Pan-Robotics/Robust-IO-Expander/Robust IO Expander/Docs/Photos/3D 2.png

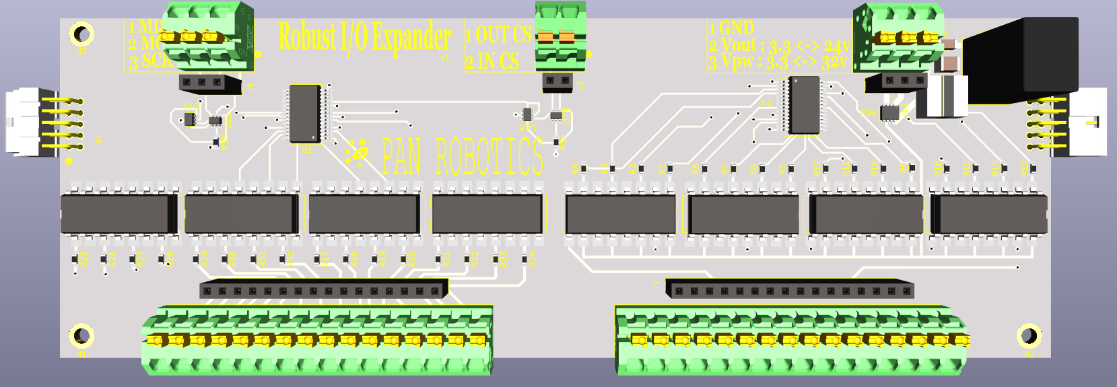
Robust IO Expander/Docs/Photos/3D 2.png
