Pan-Robotics/Robust-IO-Expander/Robust IO Expander/Docs/Photos/3D 3.png

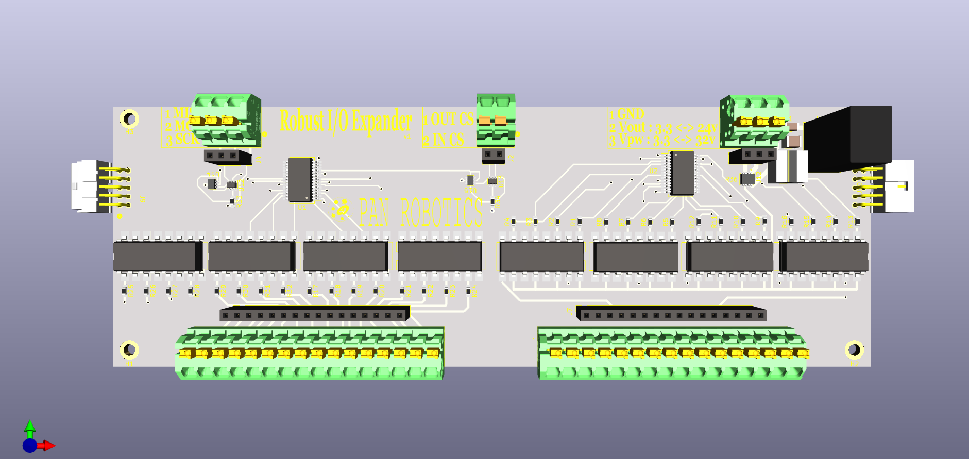
Robust IO Expander/Docs/Photos/3D 3.png
