Pan-Robotics/Robust-IO-Expander/Robust IO Expander/Docs/Photos/3D_2-clear.png

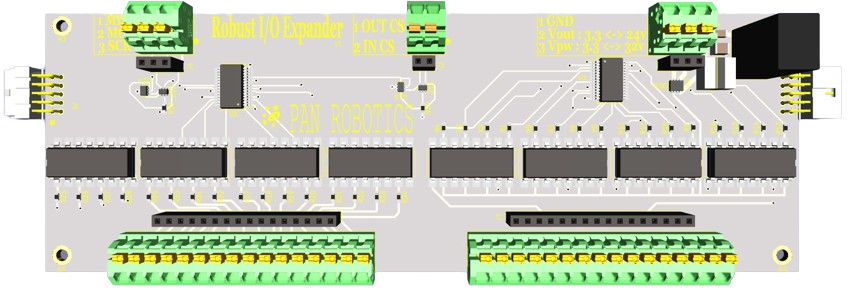
Robust IO Expander/Docs/Photos/3D_2-clear.png
