Pan-Robotics/Robust-IO-Expander/Robust IO Expander/Docs/Photos/3D_5-wacky.png

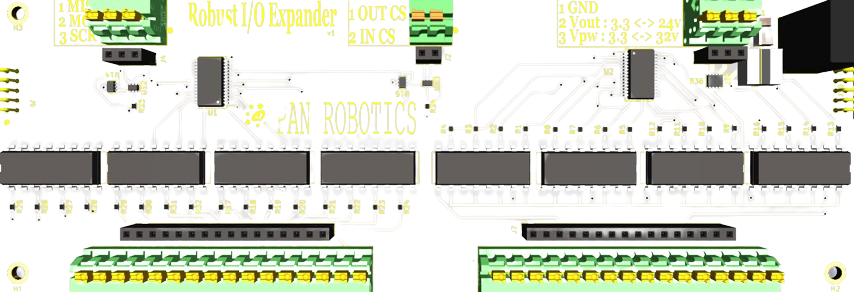
Robust IO Expander/Docs/Photos/3D_5-wacky.png
