Pan-Robotics/Robust-IO-Expander/Robust IO Expander/Docs/Photos/FreeCAD 3D 1.png

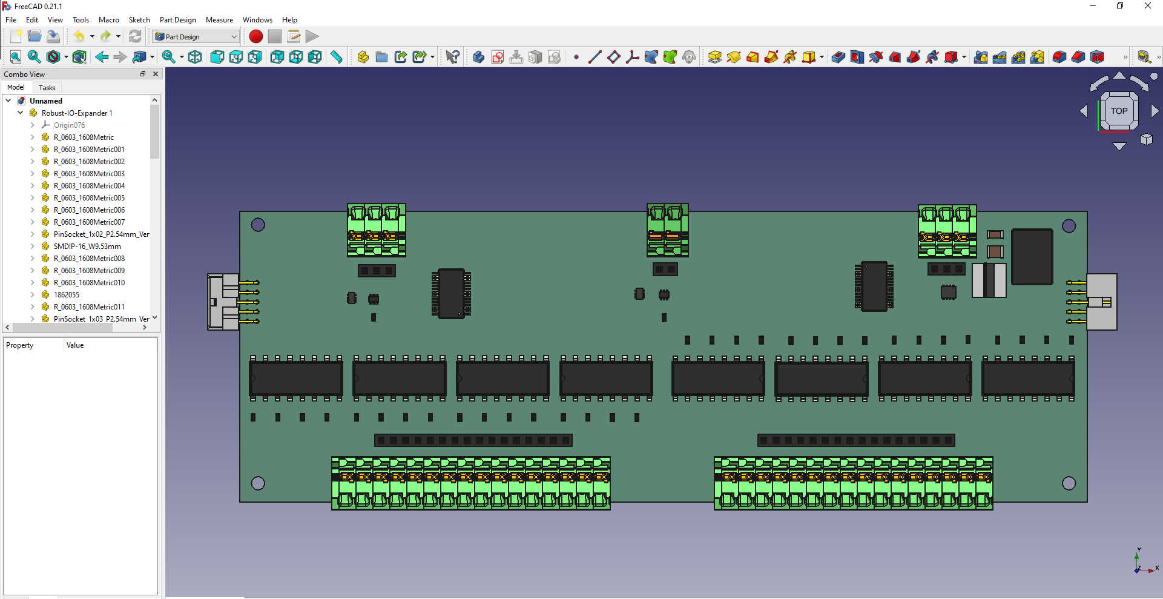
Robust IO Expander/Docs/Photos/FreeCAD 3D 1.png
