Pan-Robotics/Robust-IO-Expander/Robust IO Expander/Docs/Photos/IO-Expander 2-Back.jpg

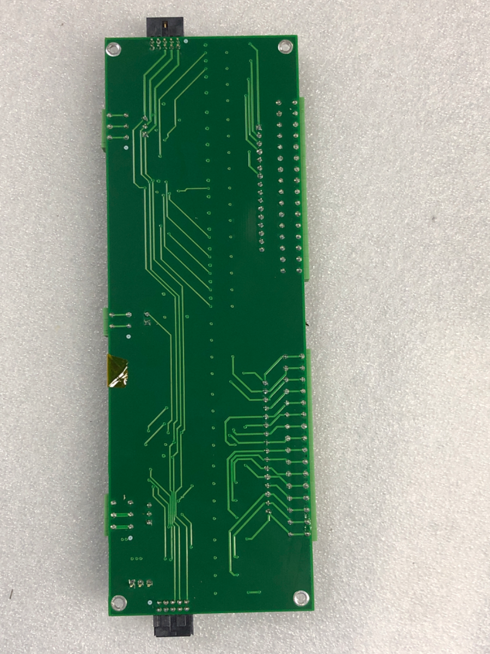
Robust IO Expander/Docs/Photos/IO-Expander 2-Back.jpg
