Pan-Robotics/Robust-IO-Expander/Robust IO Expander/Docs/Photos/IO-Expander 3.jpg

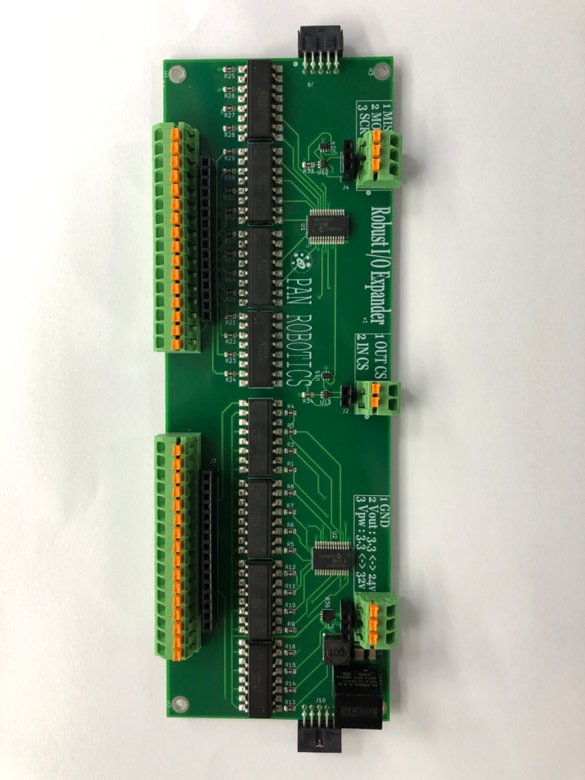
Robust IO Expander/Docs/Photos/IO-Expander 3.jpg
