Pan-Robotics/Robust-IO-Expander/Robust IO Expander/Docs/Photos/IO-Expander-Back.jpg

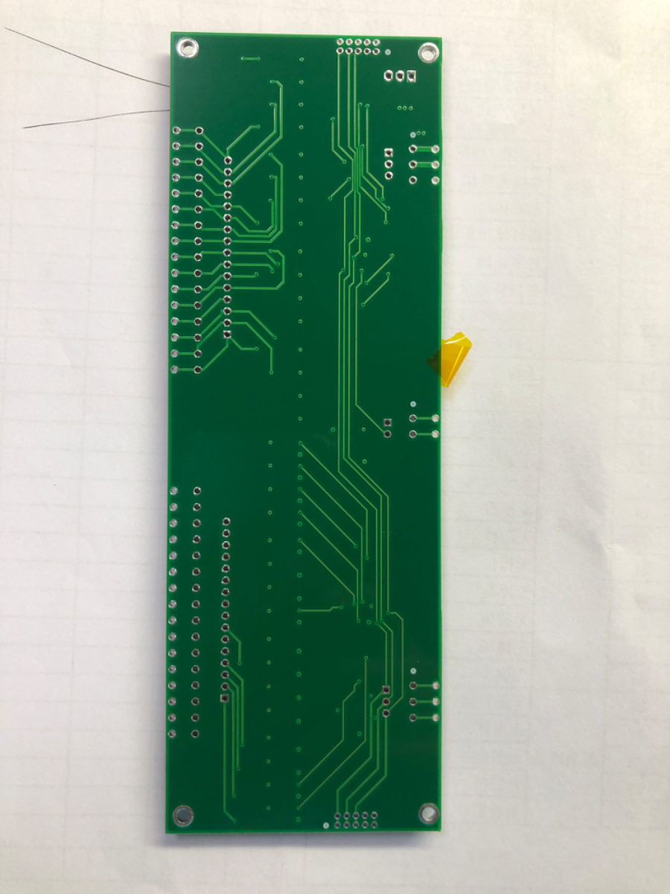
Robust IO Expander/Docs/Photos/IO-Expander-Back.jpg
