Pan-Robotics/Robust-IO-Expander/Robust IO Expander/Docs/Photos/IO-Expander-Clear.png

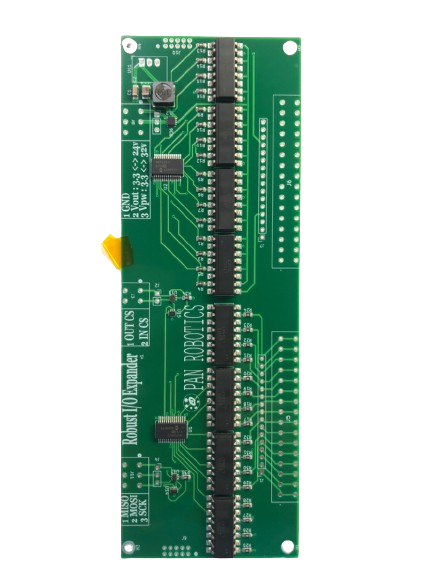
Robust IO Expander/Docs/Photos/IO-Expander-Clear.png
