Pan-Robotics/Robust-IO-Expander/Robust IO Expander/Docs/Photos/PCB 1.png

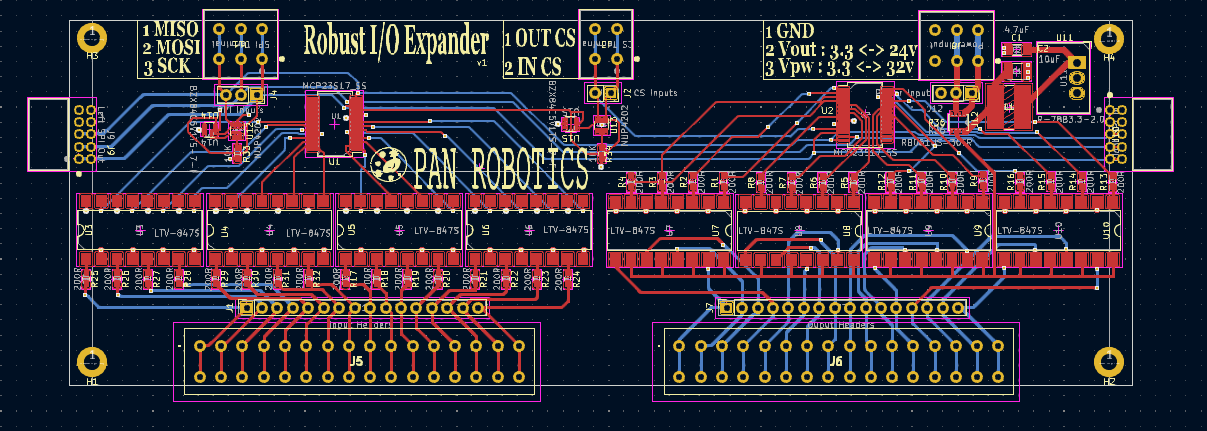
Robust IO Expander/Docs/Photos/PCB 1.png
